alinguuu/ESP32-SmartIrrigation/assets/3d-files/bananapi-case-bottom-fan.png

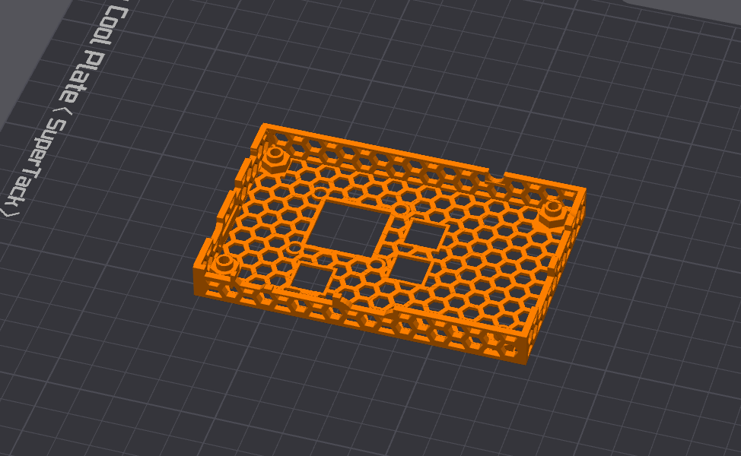
assets/3d-files/bananapi-case-bottom-fan.png
