alinguuu/ESP32-SmartIrrigation/assets/3d-files/bananapi-case-top.png

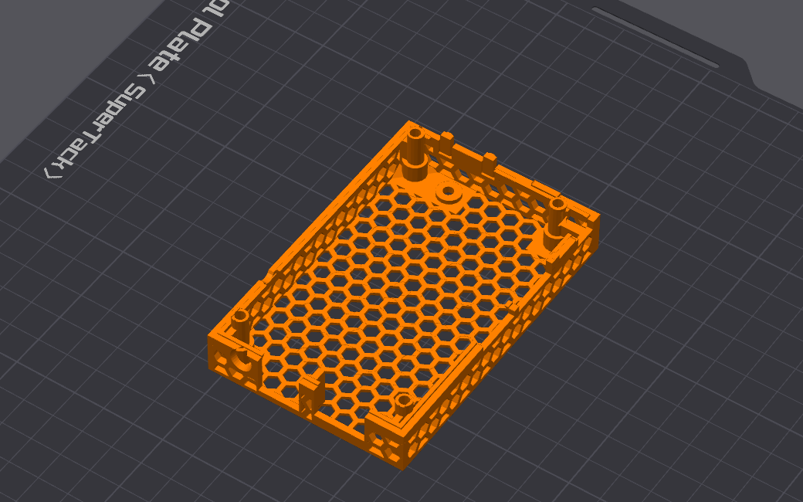
assets/3d-files/bananapi-case-top.png
