alinguuu/ESP32-SmartIrrigation/assets/3d-files/cable-box-cover-small.png

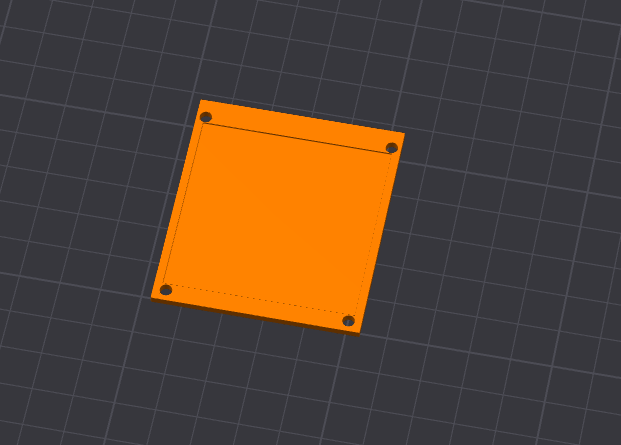
assets/3d-files/cable-box-cover-small.png
