alinguuu/ESP32-SmartIrrigation/assets/3d-files/cable-junction-box-small.png

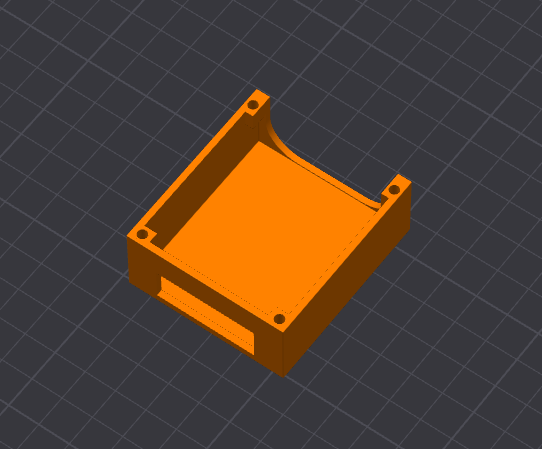
assets/3d-files/cable-junction-box-small.png
