alinguuu/ESP32-SmartIrrigation/assets/3d-files/fan-grille.png

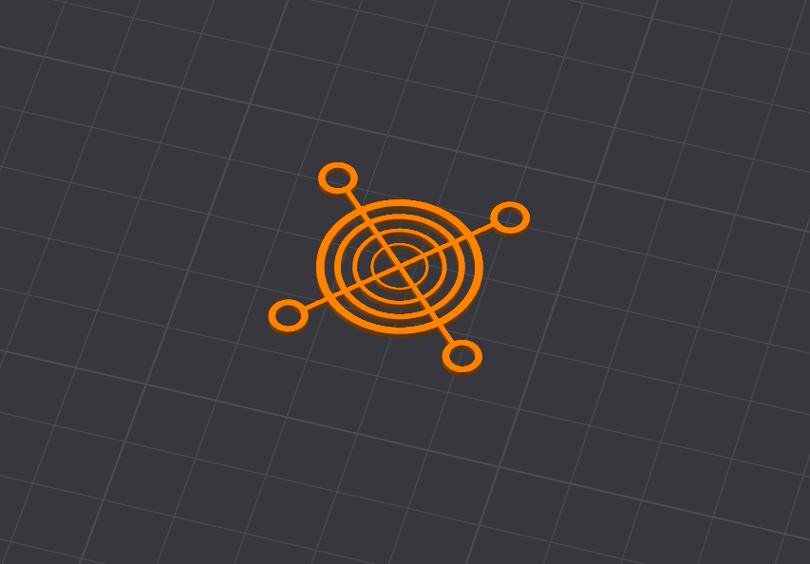
assets/3d-files/fan-grille.png
