alinguuu/ESP32-SmartIrrigation/assets/3d-files/main-mounting-plate.png

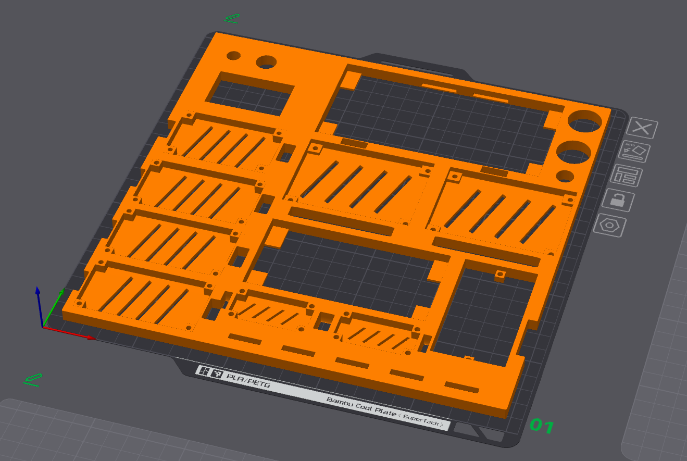
assets/3d-files/main-mounting-plate.png
