alinguuu/ESP32-SmartIrrigation/assets/3d-files/mosfet-driver-plate.png

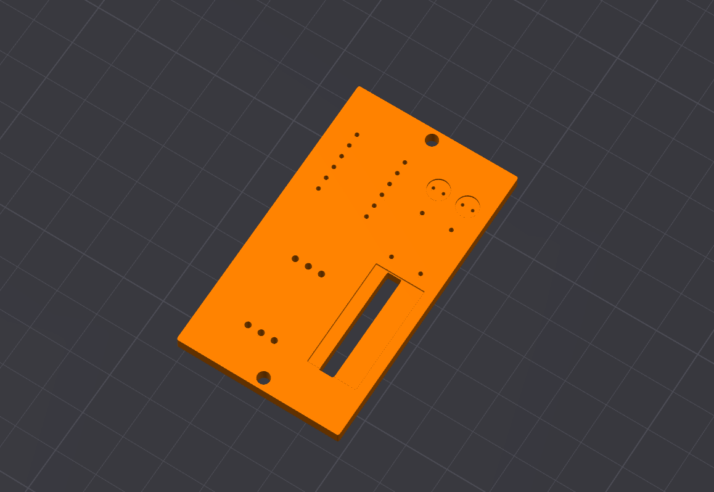
assets/3d-files/mosfet-driver-plate.png
