alinguuu/ESP32-SmartIrrigation/assets/3d-files/soil-sensor-cap.png

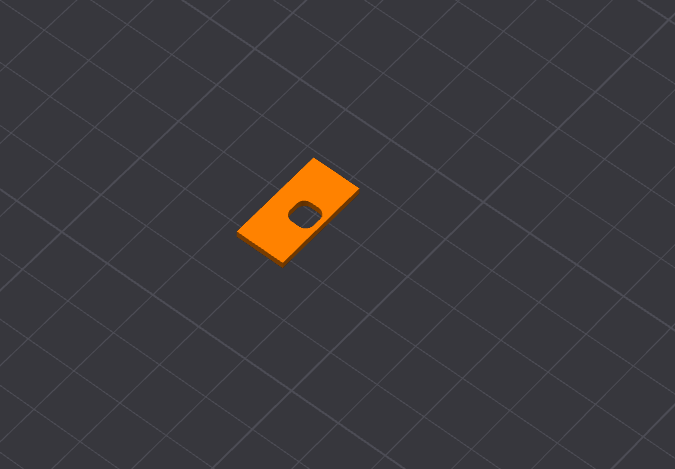
assets/3d-files/soil-sensor-cap.png
