alinguuu/ESP32-SmartIrrigation/assets/3d-files/soil-sensor-casing.png

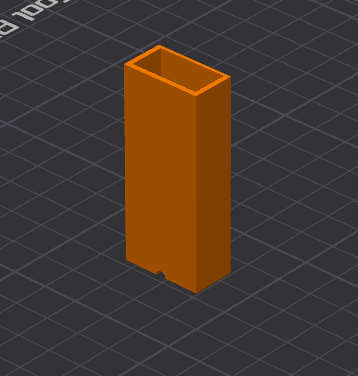
assets/3d-files/soil-sensor-casing.png
