alinguuu/ESP32-SmartIrrigation/assets/3d-files/valve-enclosure-main.png

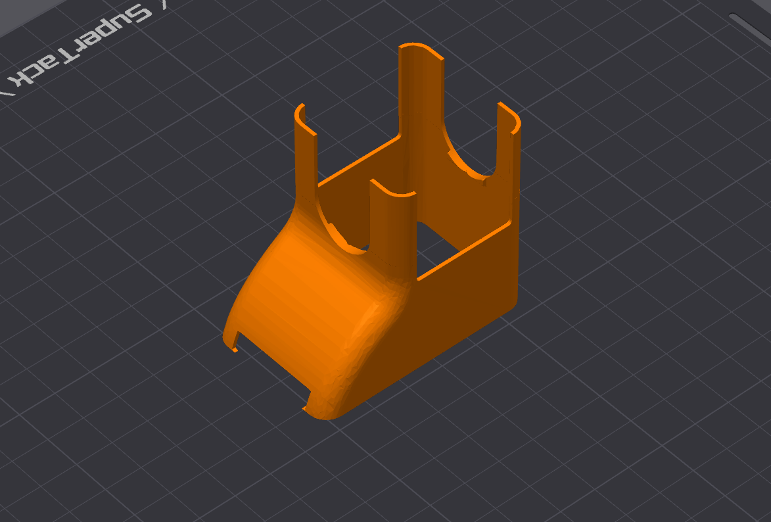
assets/3d-files/valve-enclosure-main.png
