alinguuu/ESP32-SmartIrrigation/assets/3d-files/valve-mount-plate.png

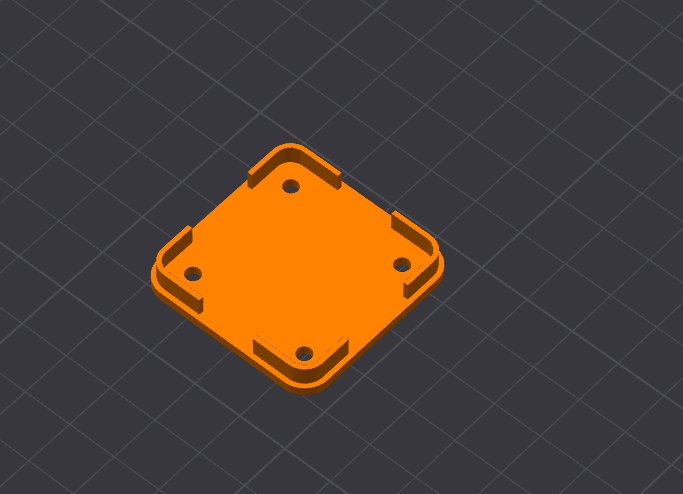
assets/3d-files/valve-mount-plate.png
