alinguuu/ESP32-SmartIrrigation/assets/3d-files/valve-top-cover-led.png

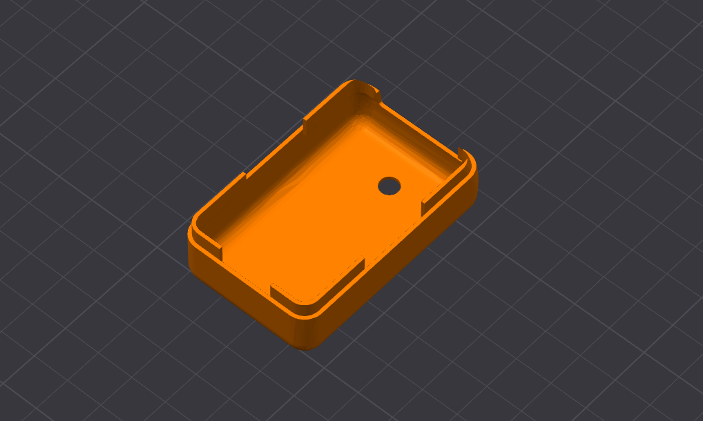
assets/3d-files/valve-top-cover-led.png
