alinguuu/ESP32-SmartIrrigation/assets/photo-gallery/bare-solenoid-valve.jpeg

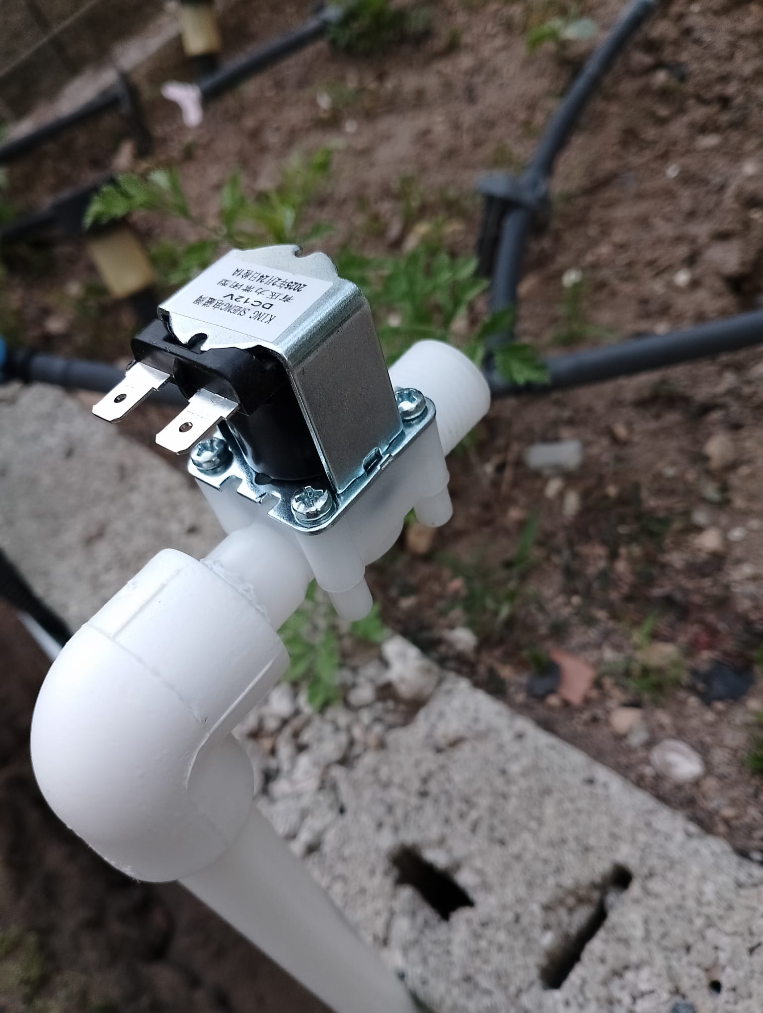
assets/photo-gallery/bare-solenoid-valve.jpeg
