alinguuu/ESP32-SmartIrrigation/assets/photo-gallery/box-back-mount.jpeg

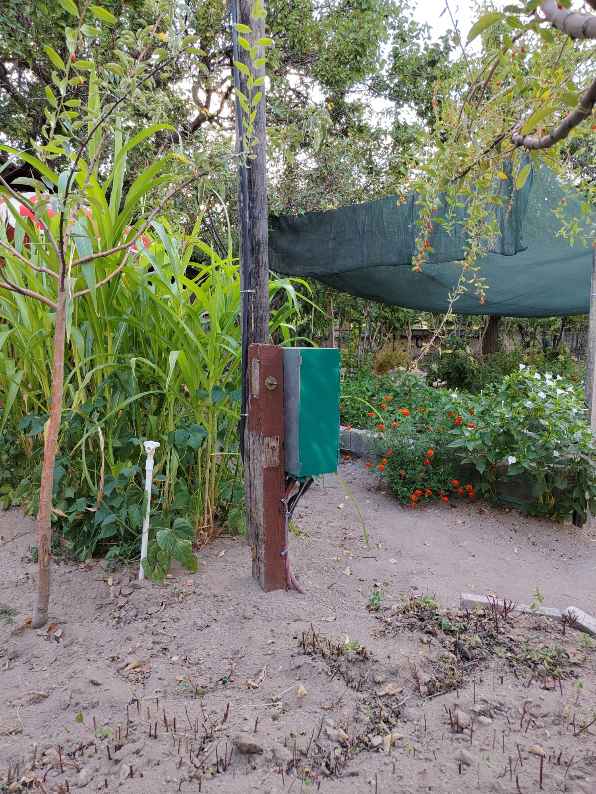
assets/photo-gallery/box-back-mount.jpeg
