alinguuu/ESP32-SmartIrrigation/assets/photo-gallery/box-enclosure-closed.jpeg

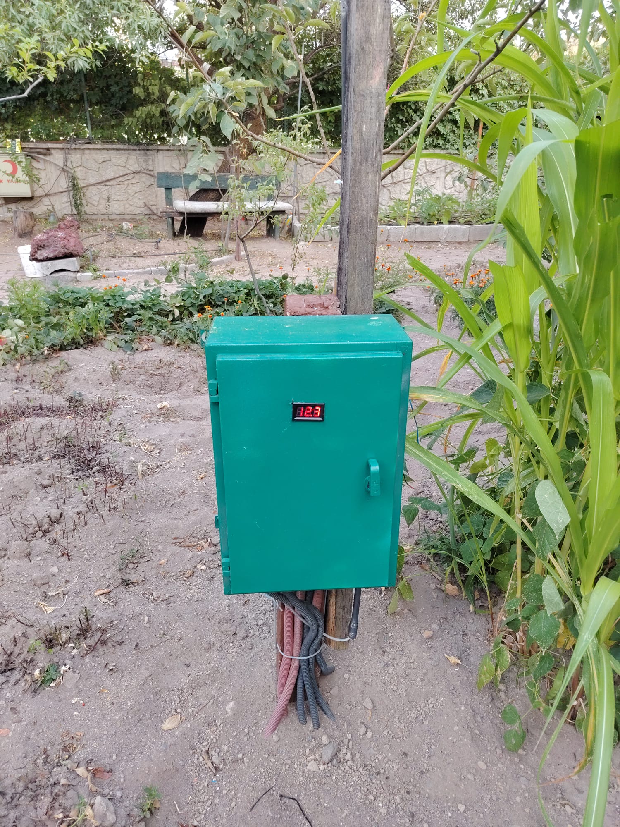
assets/photo-gallery/box-enclosure-closed.jpeg
