alinguuu/ESP32-SmartIrrigation/assets/photo-gallery/box-enclosure-open.jpeg

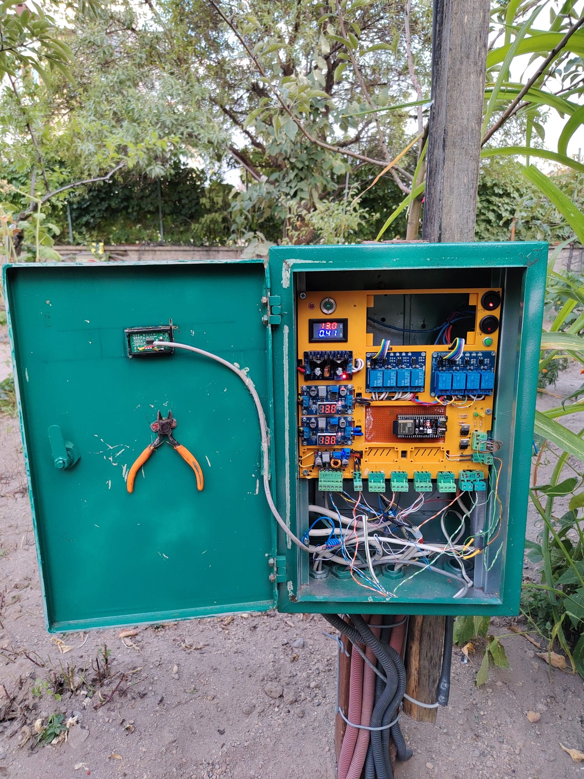
assets/photo-gallery/box-enclosure-open.jpeg
