alinguuu/ESP32-SmartIrrigation/assets/photo-gallery/box-esp32-mainboard.jpeg

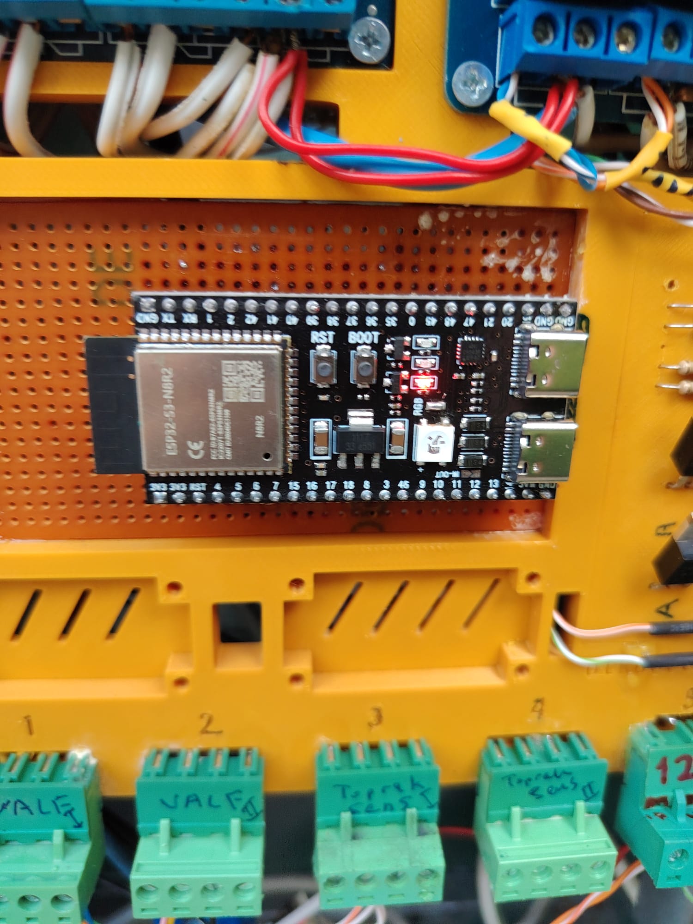
assets/photo-gallery/box-esp32-mainboard.jpeg
