alinguuu/ESP32-SmartIrrigation/assets/photo-gallery/box-mosfet.jpeg

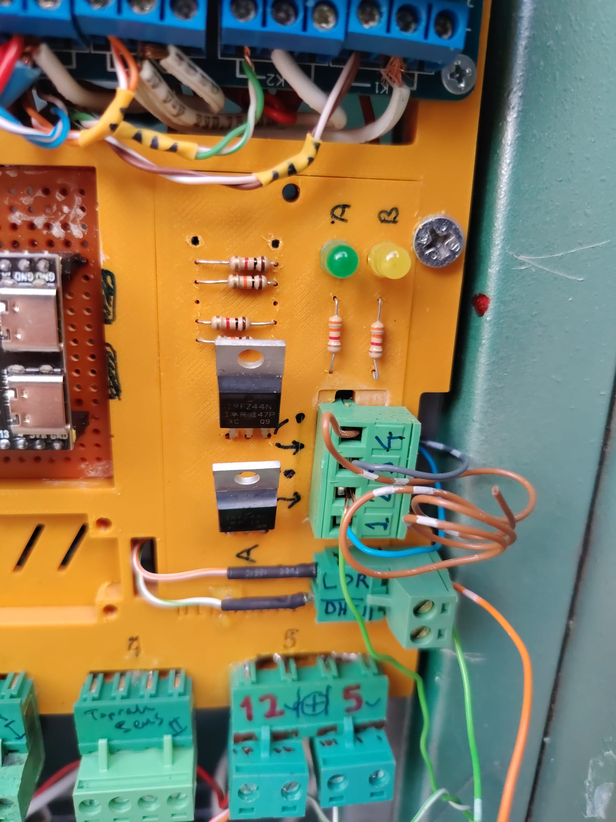
assets/photo-gallery/box-mosfet.jpeg
