alinguuu/ESP32-SmartIrrigation/assets/photo-gallery/box-night-lighting.jpeg

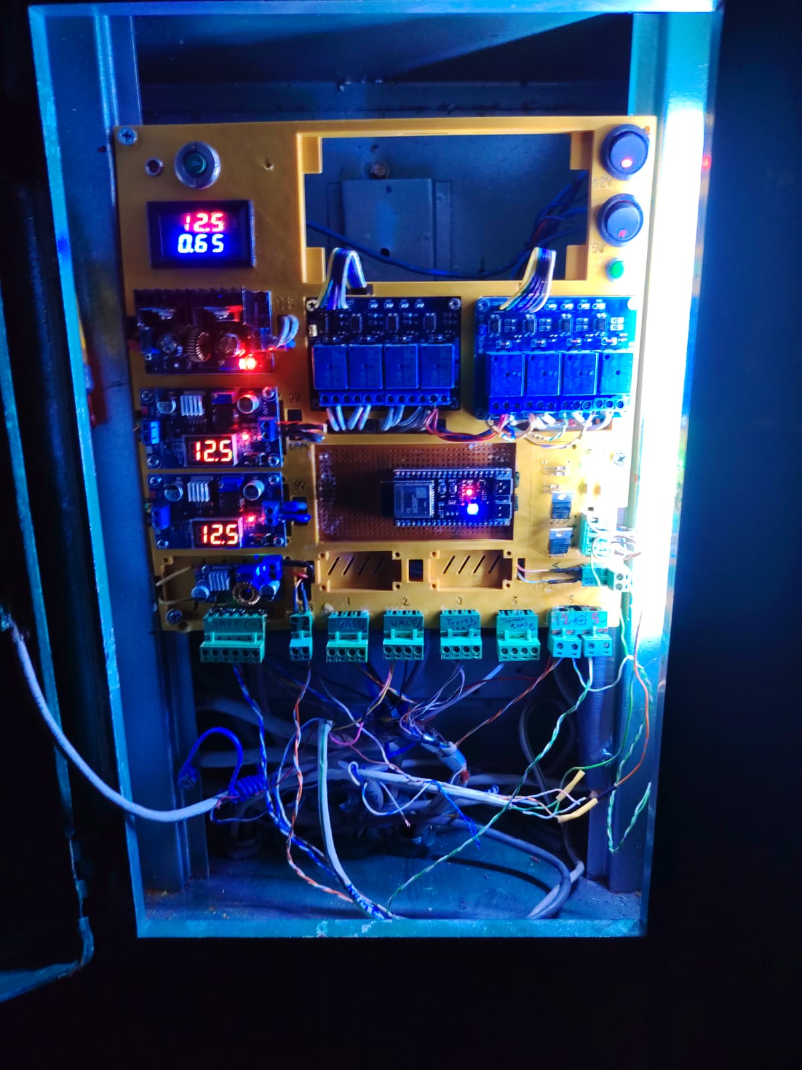
assets/photo-gallery/box-night-lighting.jpeg
