alinguuu/ESP32-SmartIrrigation/assets/photo-gallery/box-power-supply.jpeg

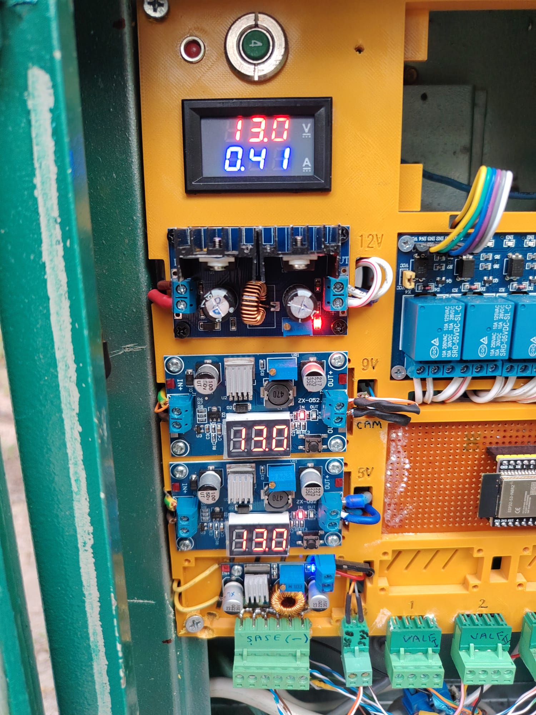
assets/photo-gallery/box-power-supply.jpeg
