alinguuu/ESP32-SmartIrrigation/assets/photo-gallery/box-relay-module.jpeg

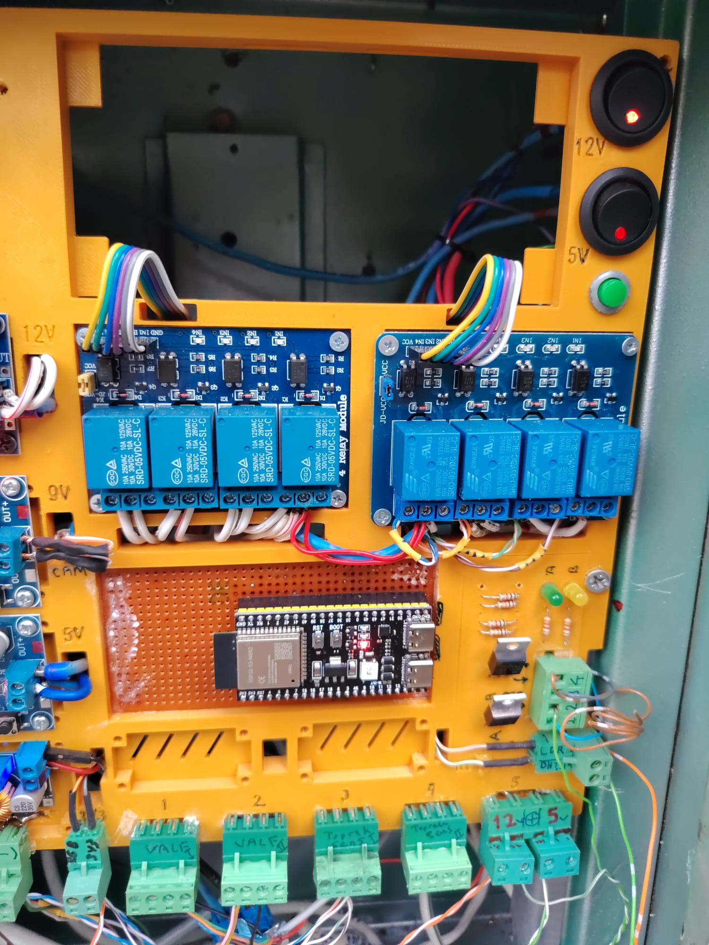
assets/photo-gallery/box-relay-module.jpeg
