alinguuu/ESP32-SmartIrrigation/assets/photo-gallery/camera.jpeg

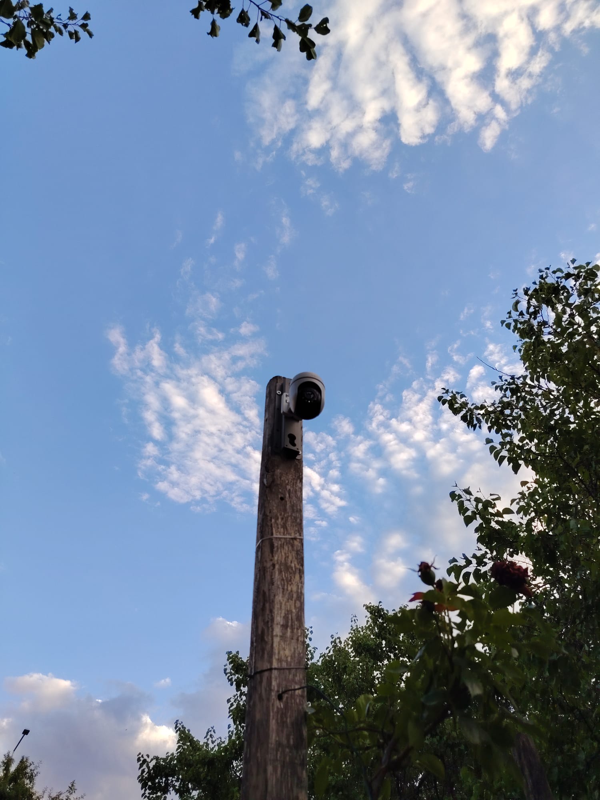
assets/photo-gallery/camera.jpeg
