alinguuu/ESP32-SmartIrrigation/assets/photo-gallery/field-night-lighting-1.jpeg

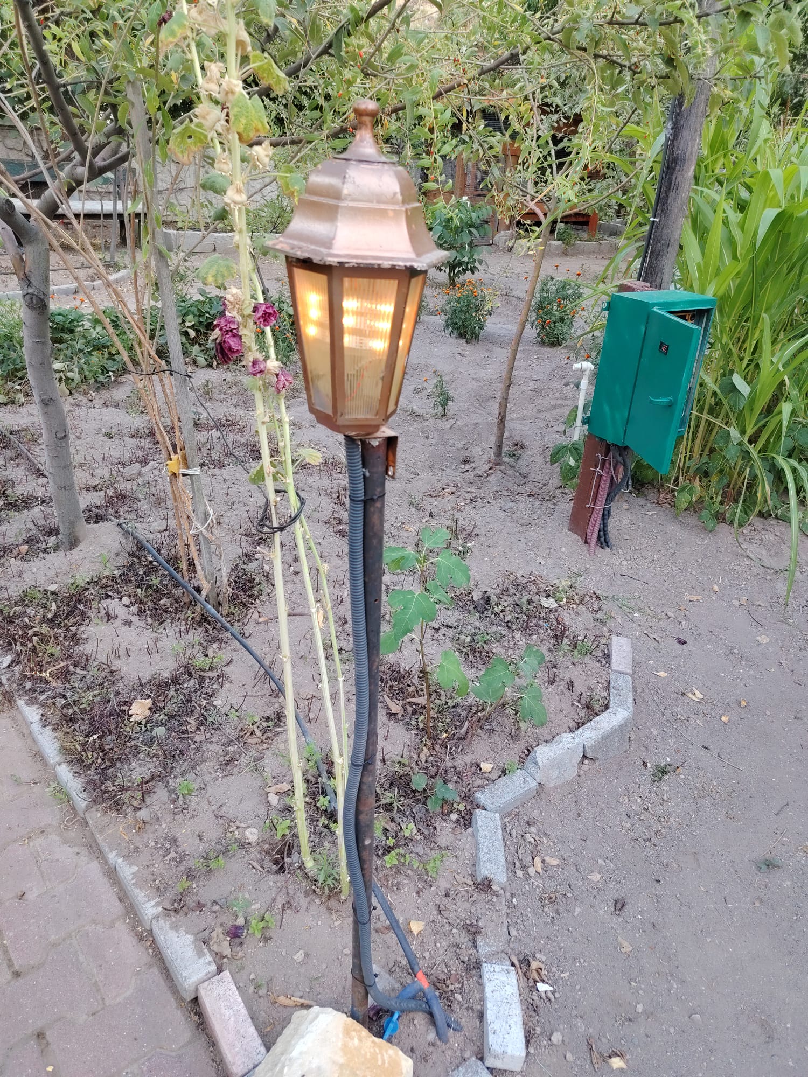
assets/photo-gallery/field-night-lighting-1.jpeg
