alinguuu/ESP32-SmartIrrigation/assets/photo-gallery/field-night-lighting-2.jpeg

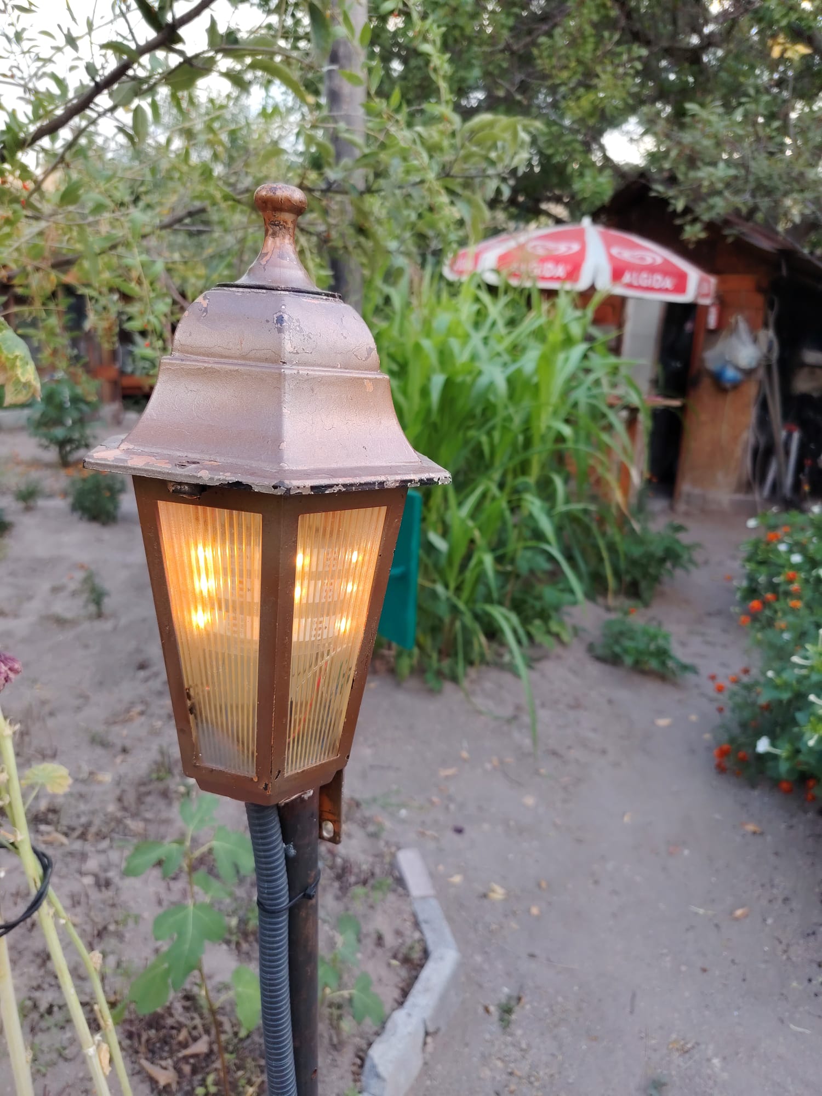
assets/photo-gallery/field-night-lighting-2.jpeg
