alinguuu/ESP32-SmartIrrigation/assets/photo-gallery/field-pipe-connection-1.jpeg

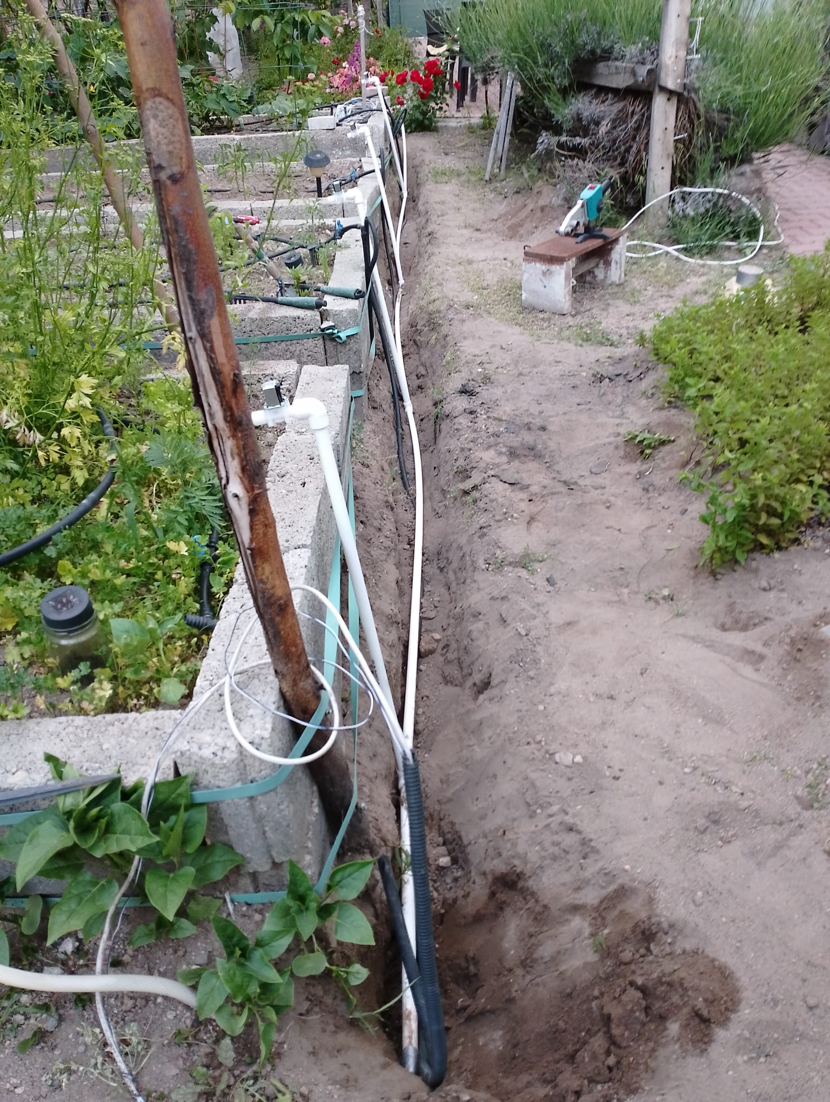
assets/photo-gallery/field-pipe-connection-1.jpeg
