alinguuu/ESP32-SmartIrrigation/assets/photo-gallery/field-pipe-connection-2.jpeg

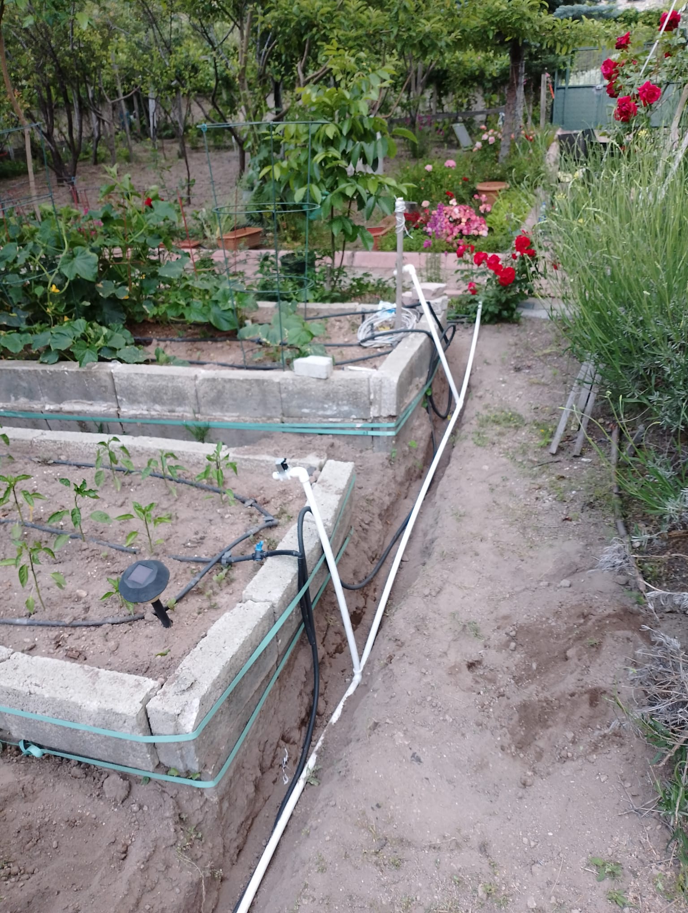
assets/photo-gallery/field-pipe-connection-2.jpeg
