alinguuu/ESP32-SmartIrrigation/assets/photo-gallery/field-pipe-connection-3.jpeg

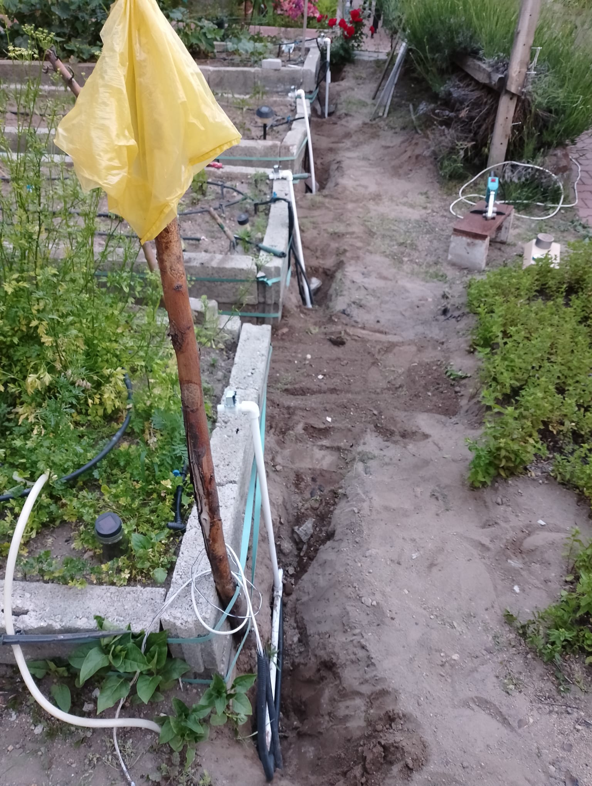
assets/photo-gallery/field-pipe-connection-3.jpeg
