alinguuu/ESP32-SmartIrrigation/assets/photo-gallery/field-solenoid-valve-02.jpeg

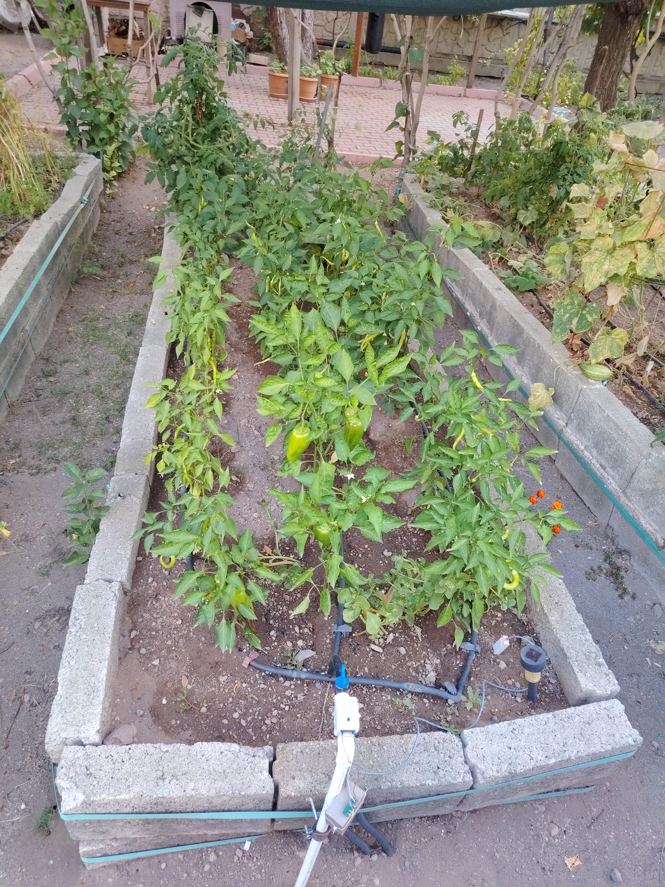
assets/photo-gallery/field-solenoid-valve-02.jpeg
