alinguuu/ESP32-SmartIrrigation/assets/photo-gallery/field-solenoid-valve-05.jpeg

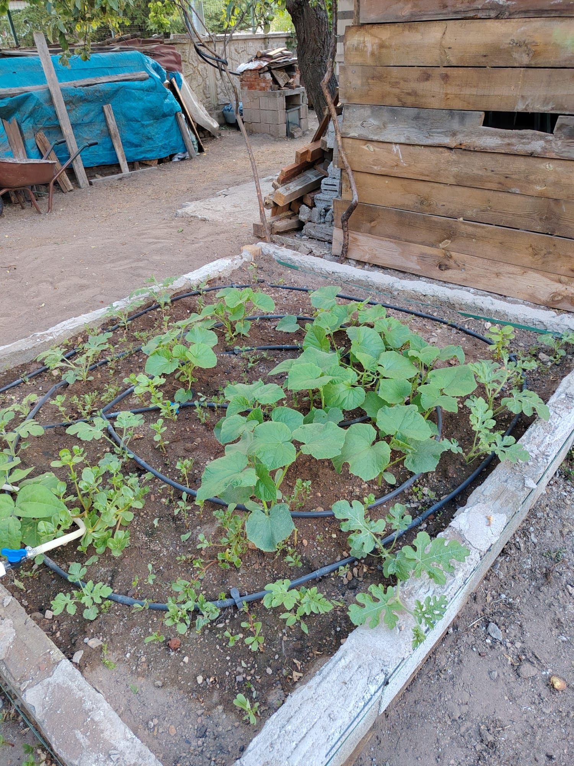
assets/photo-gallery/field-solenoid-valve-05.jpeg
