alinguuu/ESP32-SmartIrrigation/assets/photo-gallery/field-solenoid-valve-07.jpeg

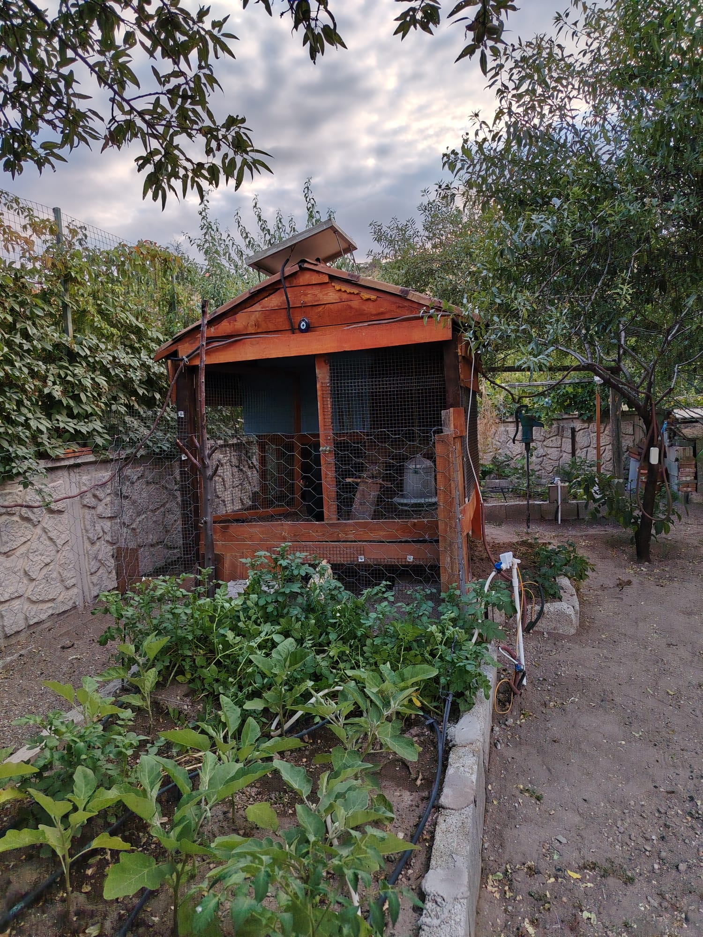
assets/photo-gallery/field-solenoid-valve-07.jpeg
