alinguuu/ESP32-SmartIrrigation/assets/photo-gallery/mobile-2fa-auth.jpeg

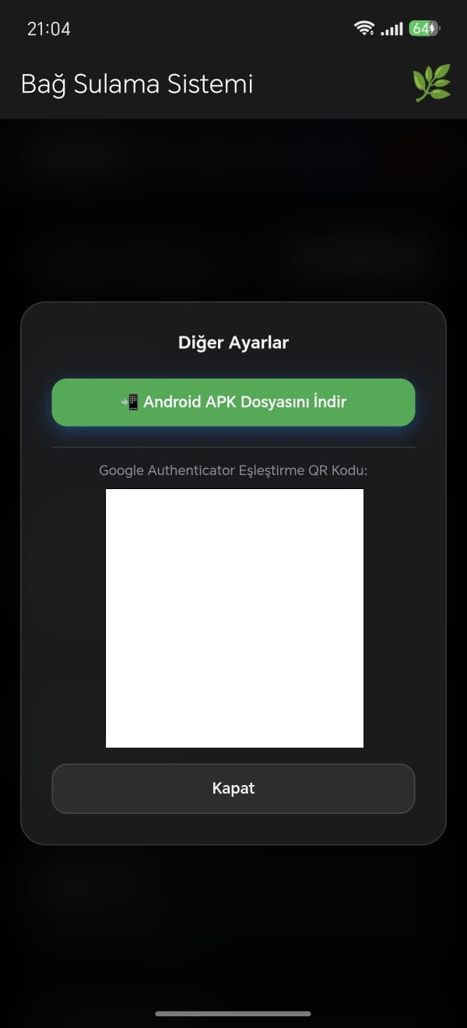
assets/photo-gallery/mobile-2fa-auth.jpeg
