alinguuu/ESP32-SmartIrrigation/assets/photo-gallery/mobile-automation-rules.jpeg

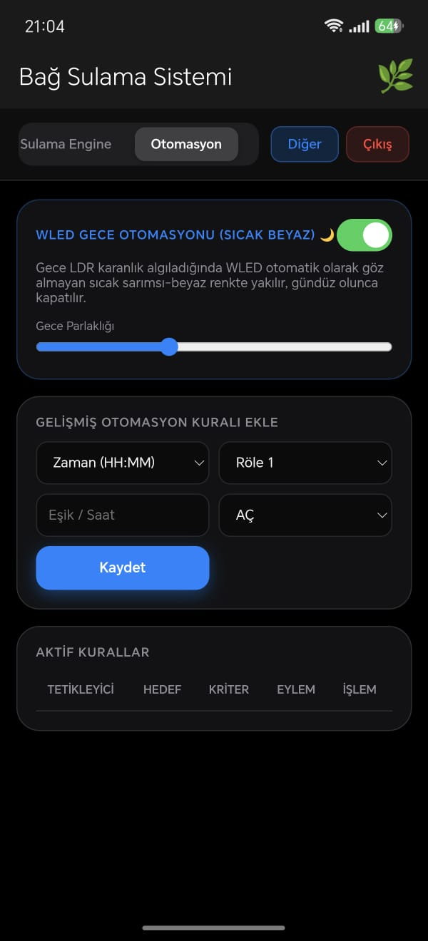
assets/photo-gallery/mobile-automation-rules.jpeg
