alinguuu/ESP32-SmartIrrigation/assets/photo-gallery/mobile-dashboard (2).jpeg

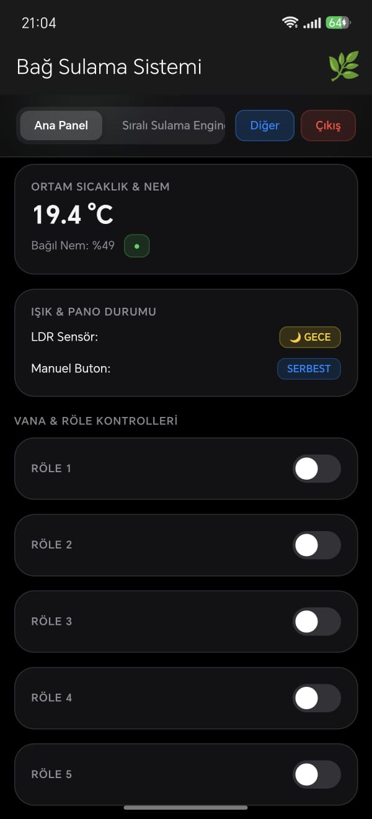
assets/photo-gallery/mobile-dashboard (2).jpeg
