alinguuu/ESP32-SmartIrrigation/assets/photo-gallery/mobile-dashboard(1).jpeg

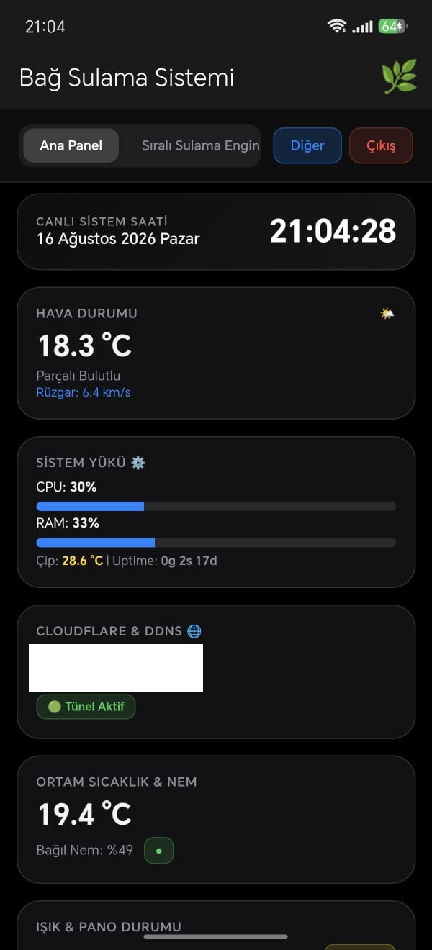
assets/photo-gallery/mobile-dashboard(1).jpeg
