alinguuu/ESP32-SmartIrrigation/assets/photo-gallery/mobile-dashboard(3).jpeg

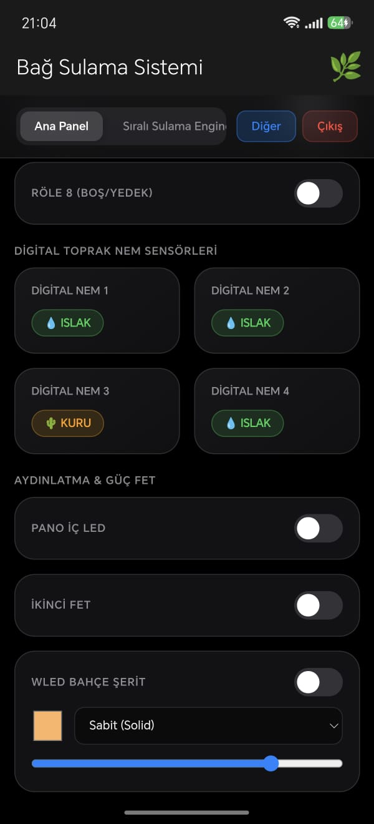
assets/photo-gallery/mobile-dashboard(3).jpeg
