alinguuu/ESP32-SmartIrrigation/assets/photo-gallery/mobile-loading-screen.jpeg

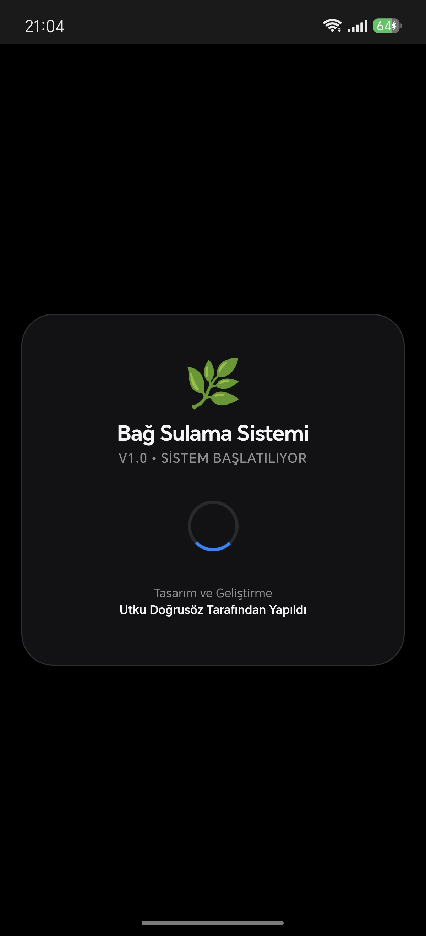
assets/photo-gallery/mobile-loading-screen.jpeg
