alinguuu/ESP32-SmartIrrigation/assets/photo-gallery/mobile-schedule-timer.jpeg

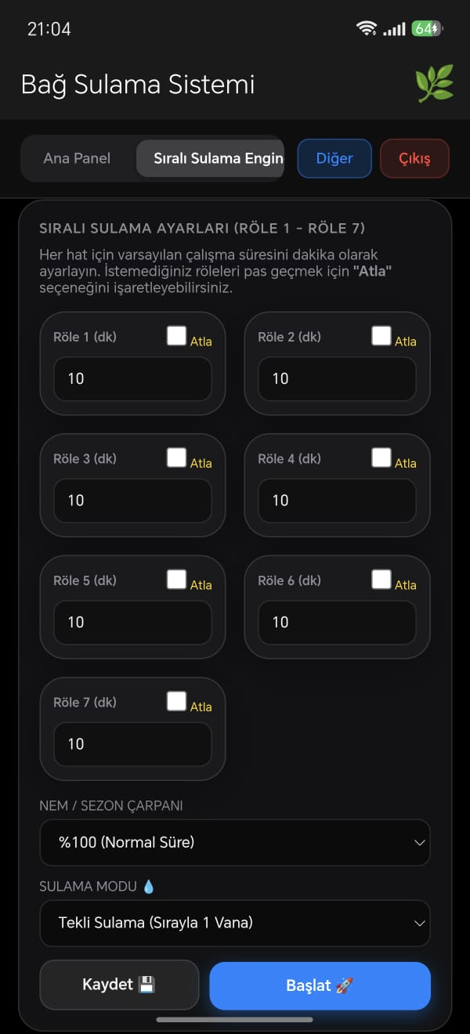
assets/photo-gallery/mobile-schedule-timer.jpeg
