alinguuu/ESP32-SmartIrrigation/assets/photo-gallery/mobile-system-logs.jpeg

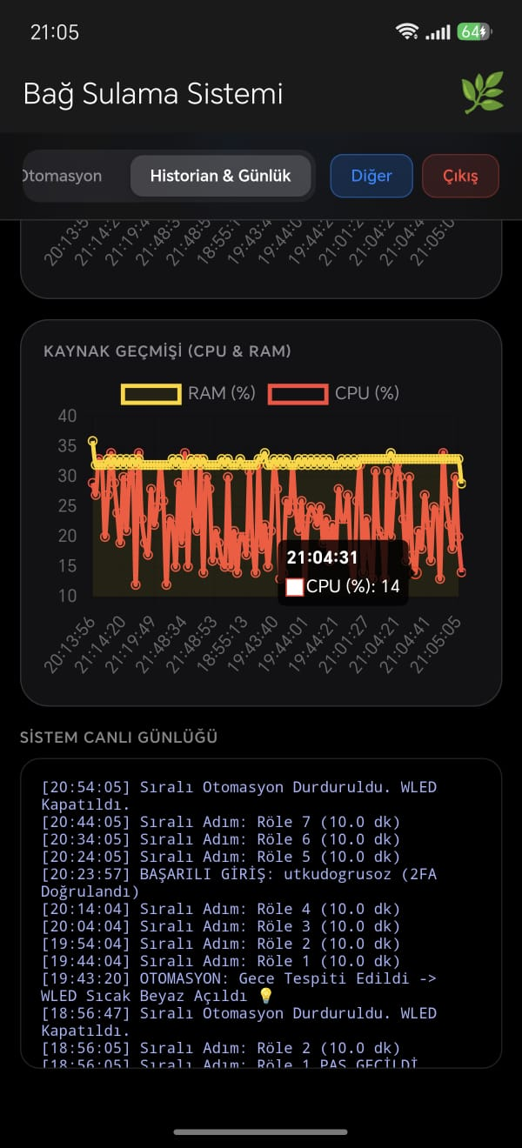
assets/photo-gallery/mobile-system-logs.jpeg
