alinguuu/ESP32-SmartIrrigation/assets/photo-gallery/mobile-system-status.jpeg

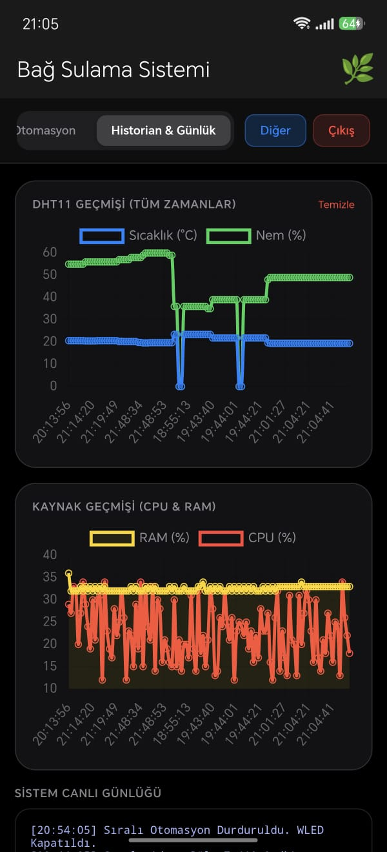
assets/photo-gallery/mobile-system-status.jpeg
