alinguuu/ESP32-SmartIrrigation/assets/photo-gallery/solenoid-valve-01.jpeg

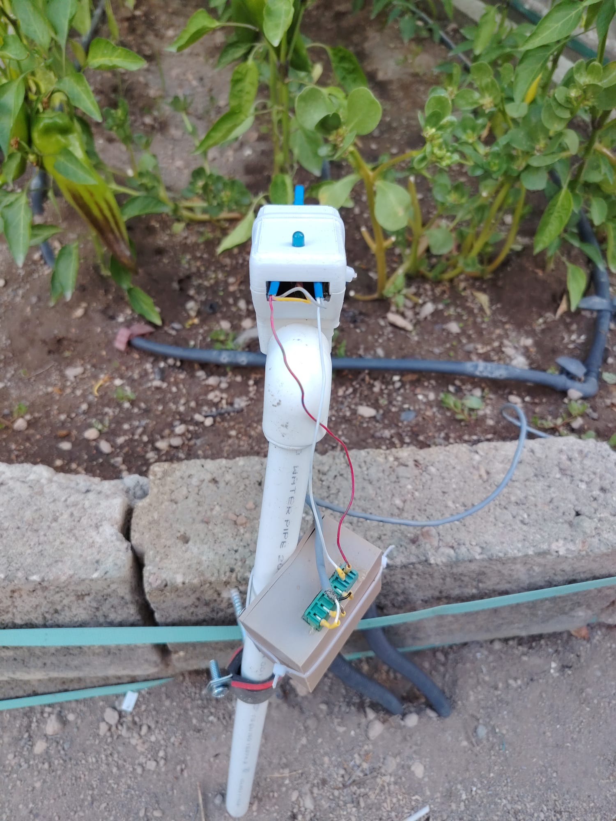
assets/photo-gallery/solenoid-valve-01.jpeg
