alinguuu/ESP32-SmartIrrigation/assets/photo-gallery/ui-automation-rules.png

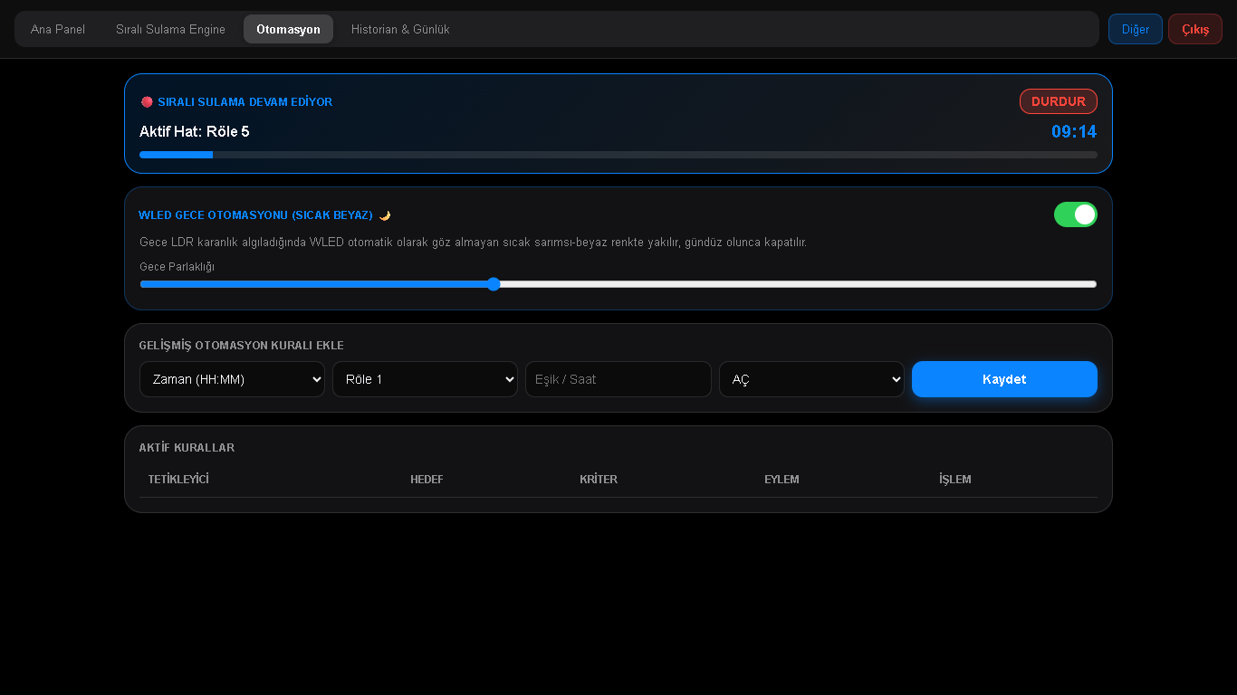
assets/photo-gallery/ui-automation-rules.png
