alinguuu/ESP32-SmartIrrigation/assets/photo-gallery/ui-login-screen.png

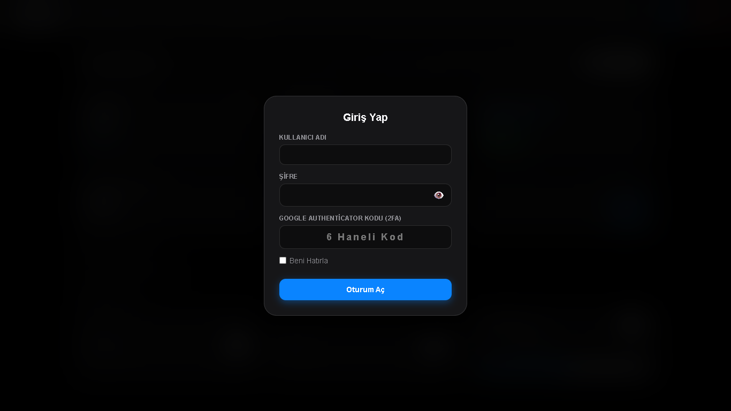
assets/photo-gallery/ui-login-screen.png
