alinguuu/ESP32-SmartIrrigation/assets/photo-gallery/ui-relay-status.png

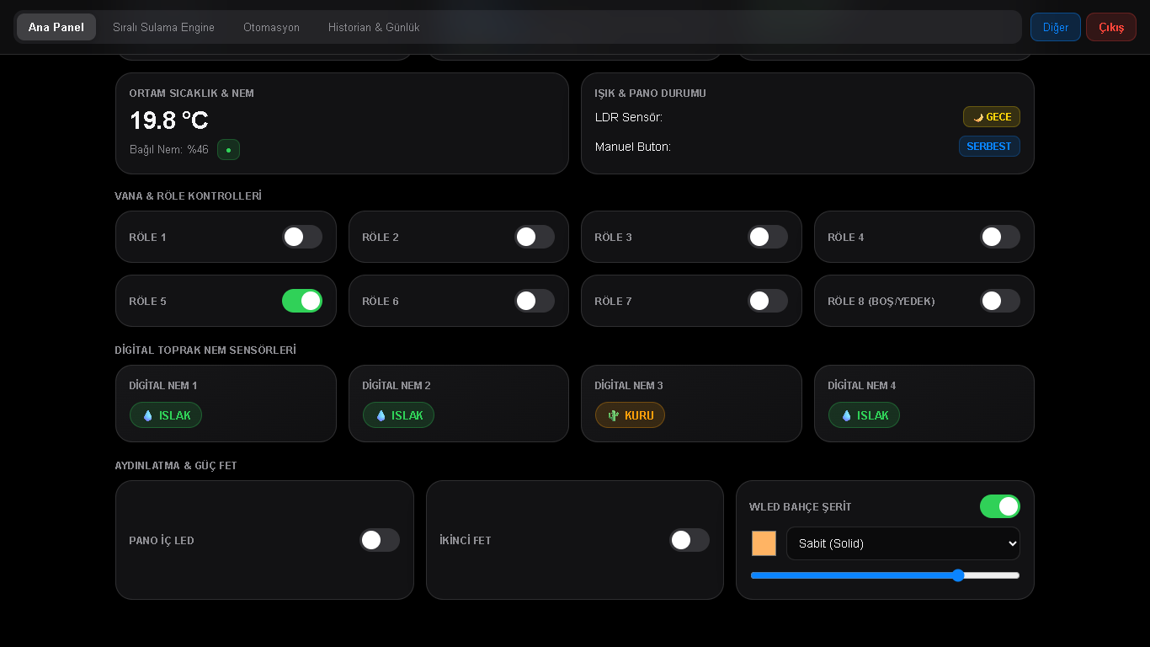
assets/photo-gallery/ui-relay-status.png
