alinguuu/ESP32-SmartIrrigation/assets/photo-gallery/ui-schedule-timer.png

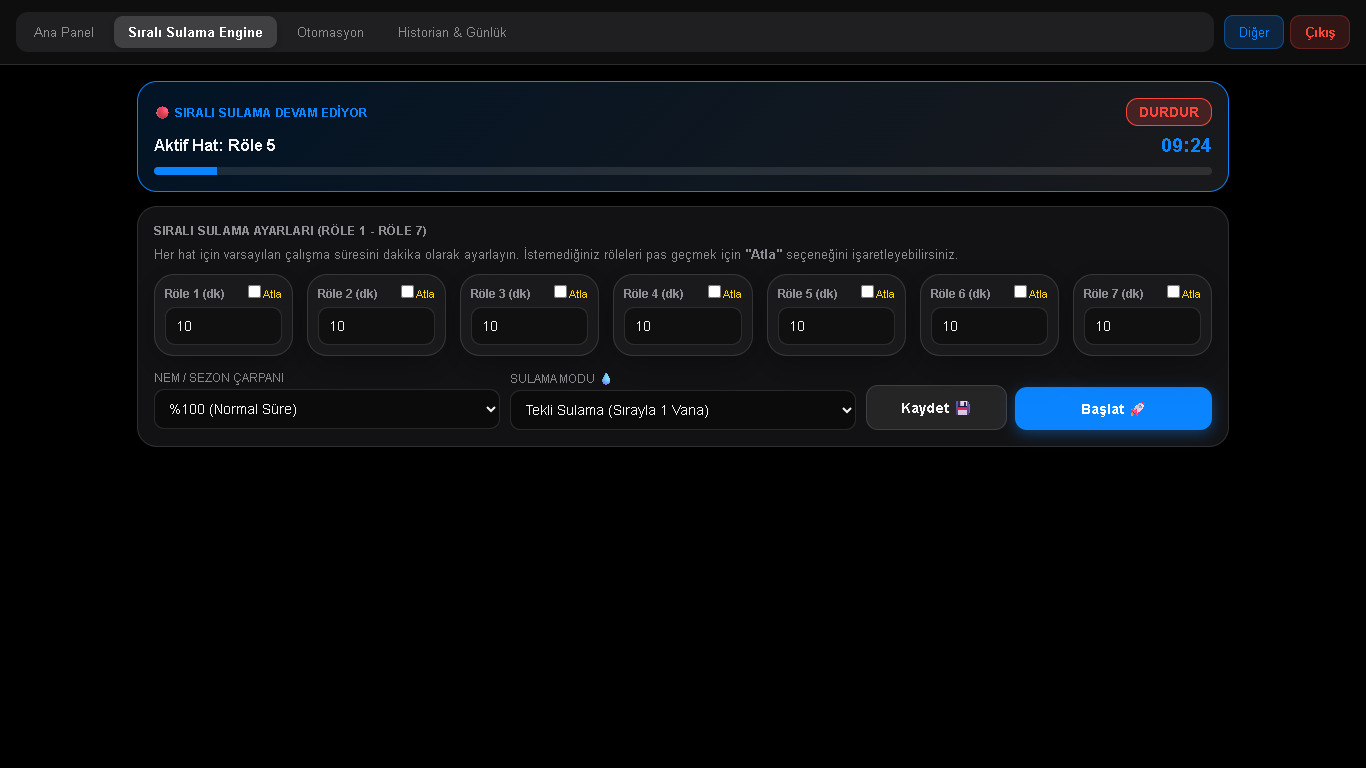
assets/photo-gallery/ui-schedule-timer.png
