alinguuu/ESP32-SmartIrrigation/assets/photo-gallery/ui-system-logs-and-status.png

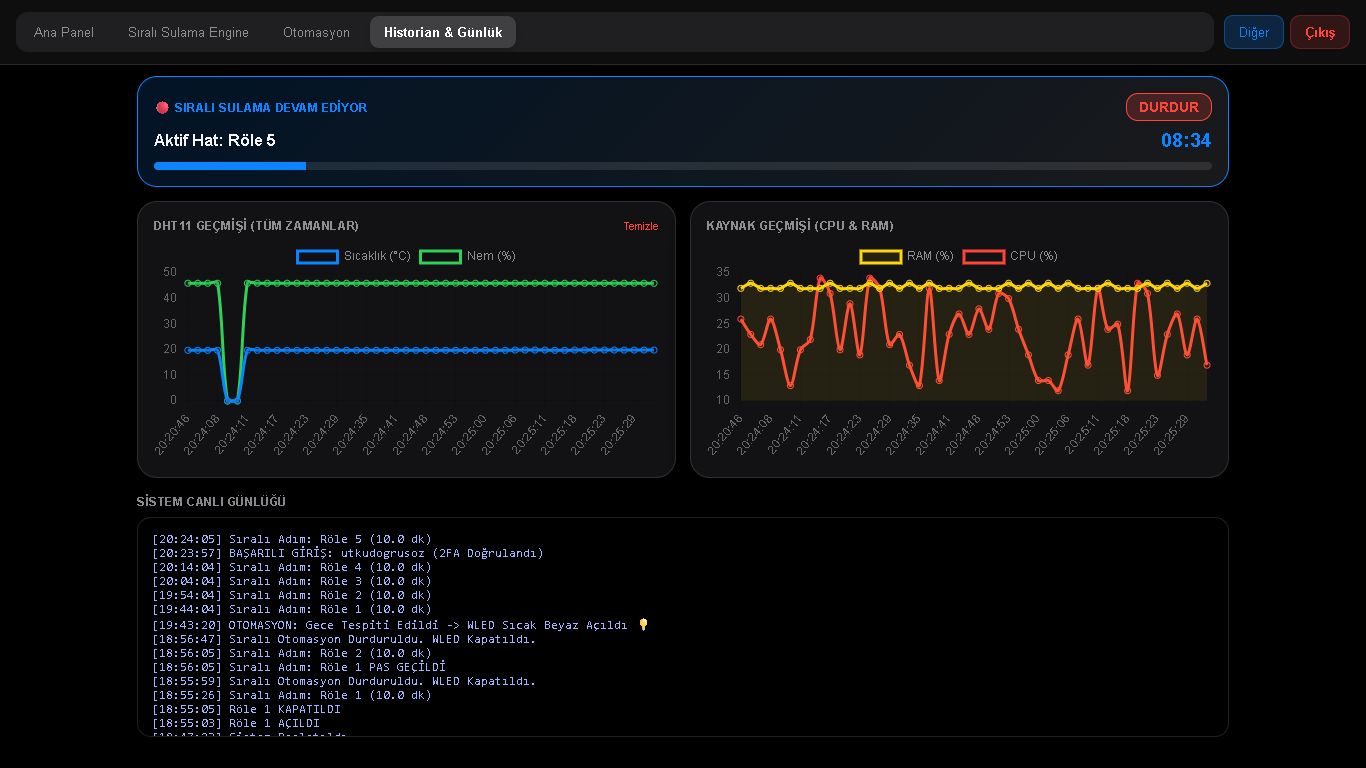
assets/photo-gallery/ui-system-logs-and-status.png
