alinguuu/ESP32-SmartIrrigation/assets/photo-gallery/watering-solenoid-valve-1.jpeg

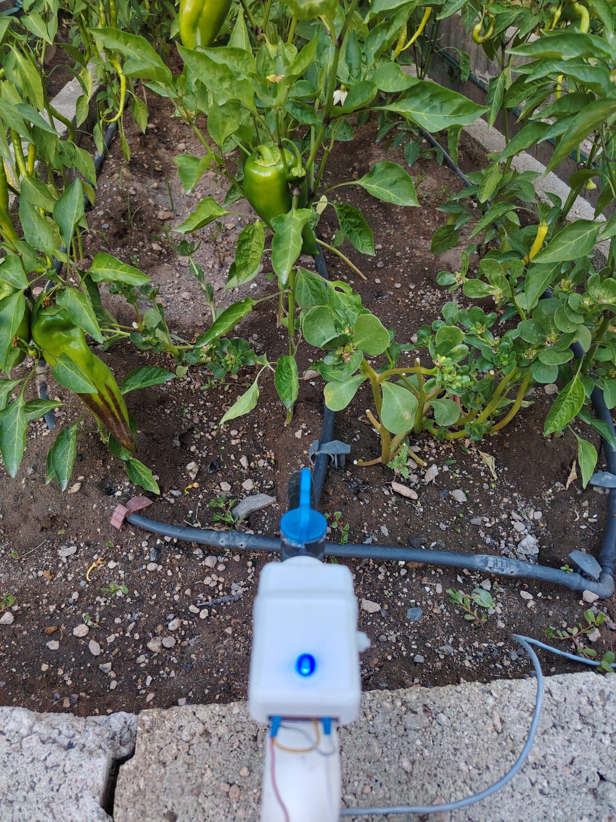
assets/photo-gallery/watering-solenoid-valve-1.jpeg
