alinguuu/ESP32-SmartIrrigation/assets/photo-gallery/watering-solenoid-valve-2.jpeg

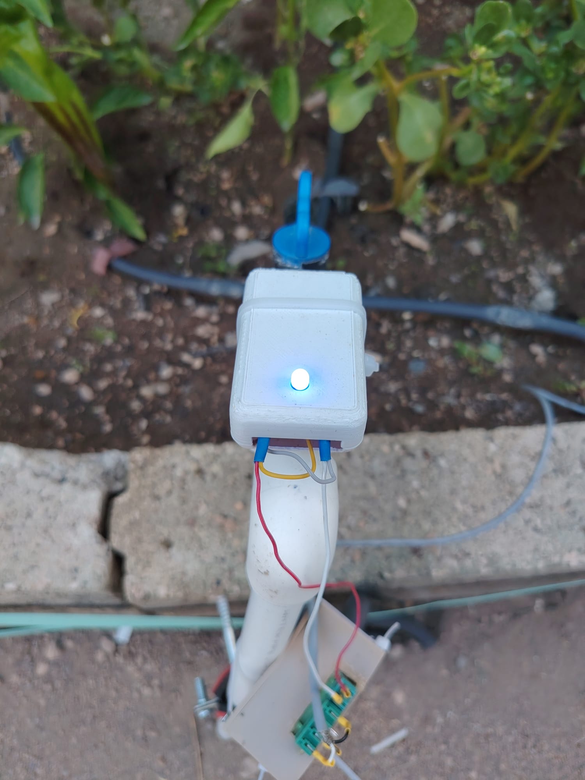
assets/photo-gallery/watering-solenoid-valve-2.jpeg
