alinguuu/ESP32-SmartIrrigation/assets/photo-gallery/web-mobile-dashboard.jpeg

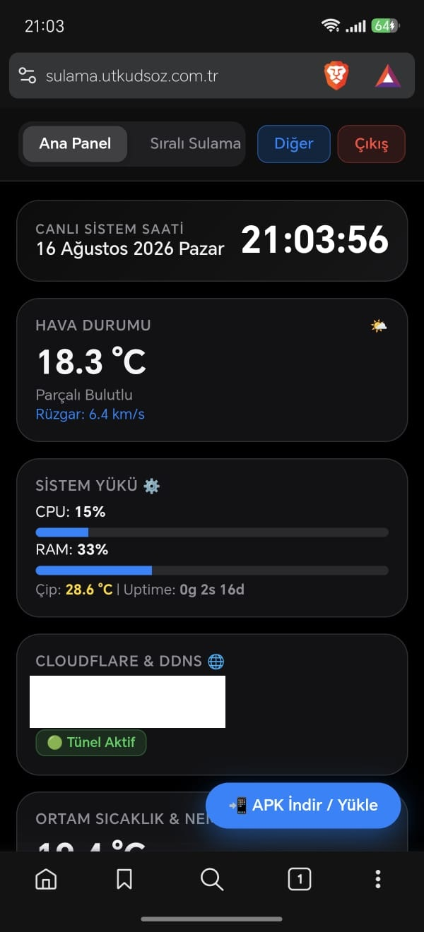
assets/photo-gallery/web-mobile-dashboard.jpeg
