alinguuu/ESP32-SmartIrrigation/assets/photo-gallery/wled-watering-mode.jpeg

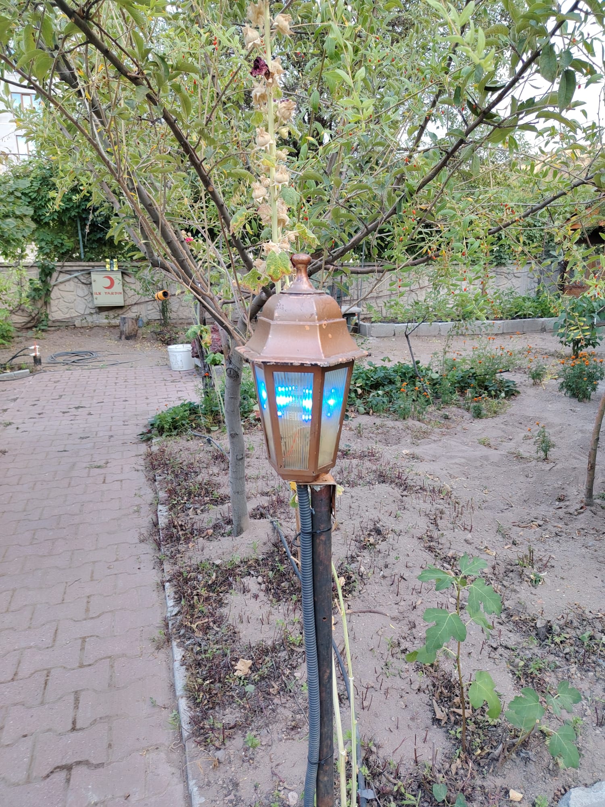
assets/photo-gallery/wled-watering-mode.jpeg
