alinguuu/ESP32-SmartIrrigation/assets/photo-gallery/box-wiring-overview.jpeg

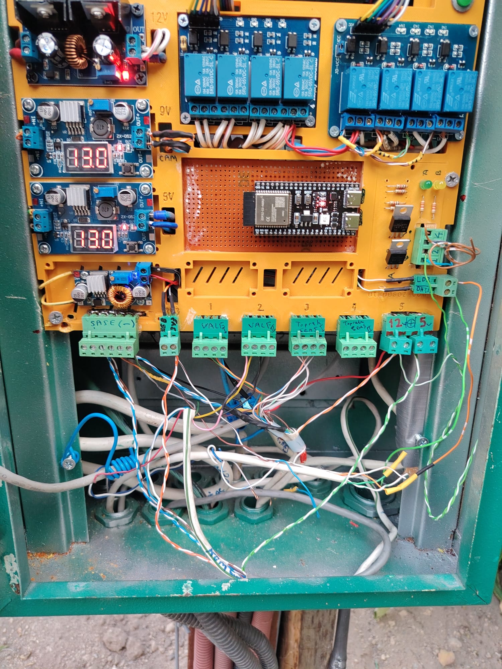
assets/photo-gallery/box-wiring-overview.jpeg
