alinguuu/ESP32-SmartIrrigation/assets/photo-gallery/field-water-valve-setup.jpeg

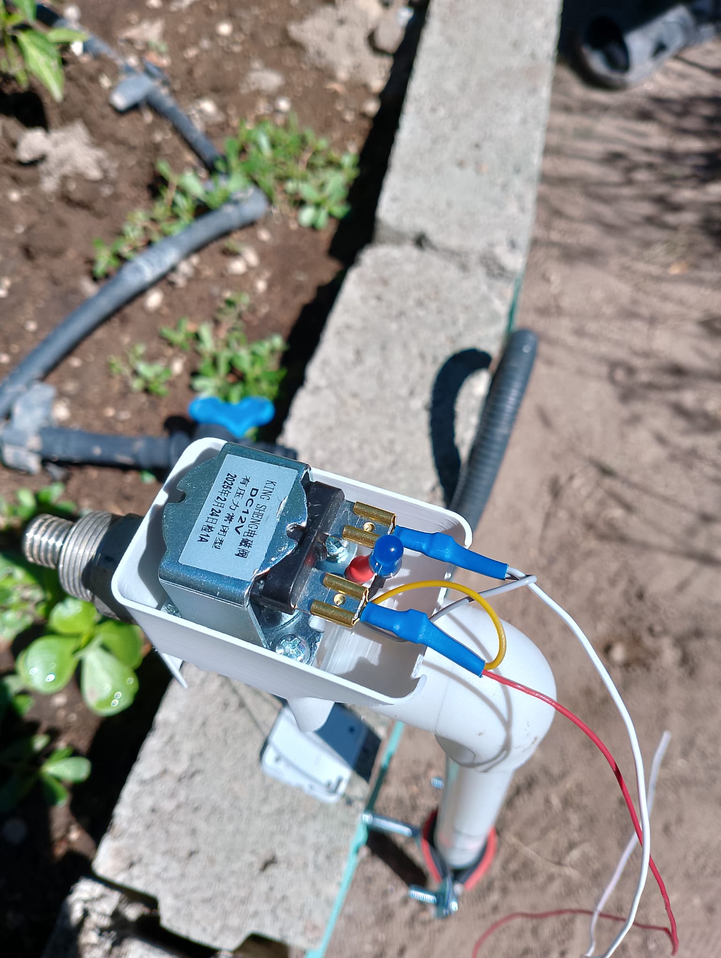
assets/photo-gallery/field-water-valve-setup.jpeg
